mentako-ya/mtk64erp/image/mtk64erp_top.jpg

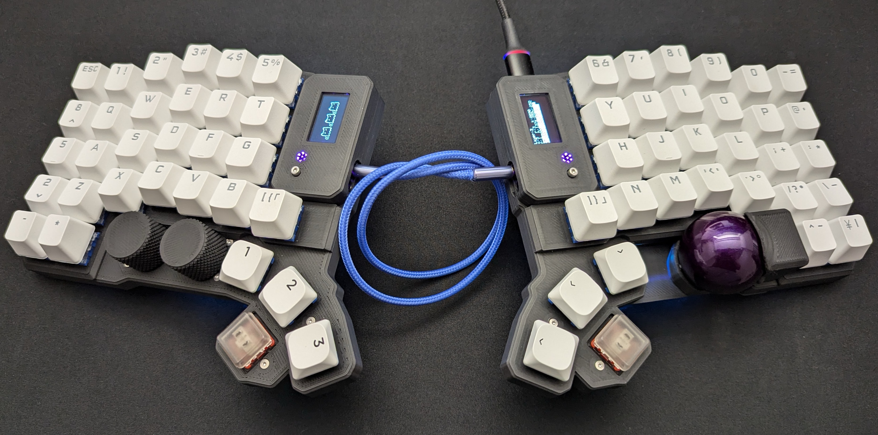
image/mtk64erp_top.jpg
