mentako-ya/mtk64erp/image/remap/remap_4.png

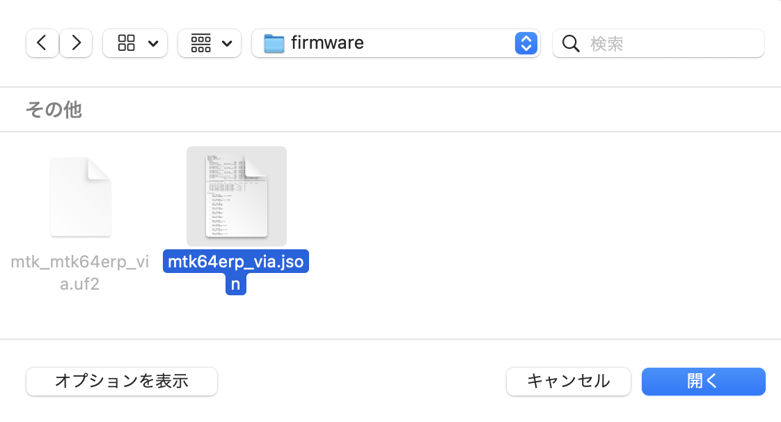
image/remap/remap_4.png
