mentako-ya/mtk64erp/casedata/mtk64erp_STL/rev1/mtk64erp_knob_19mm.stl

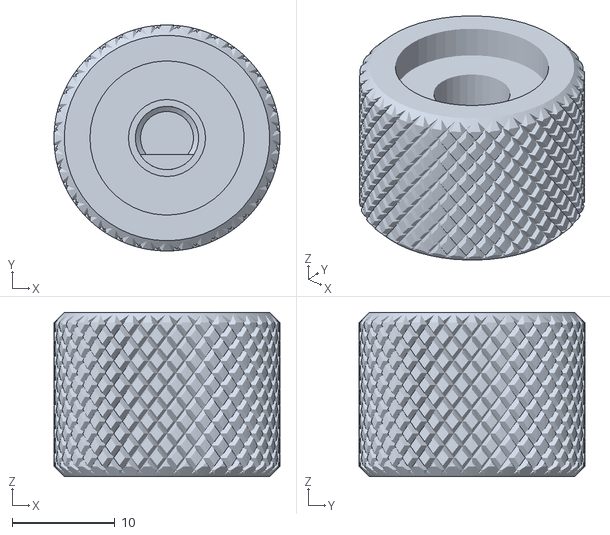
[picture p38: CAD file, 2024-08-11]
casedata/mtk64erp_STL/rev1/mtk64erp_knob_19mm.stl
22.0 x 22.0 x 16.0
